antoniojpmarin/LoRa-NBIoT-Gateway/hardware/esquematicos_tfg.kicad_sch

## KiCad design hardware/esquematicos_tfg.kicad_sch (2026-03-21, last stored version)

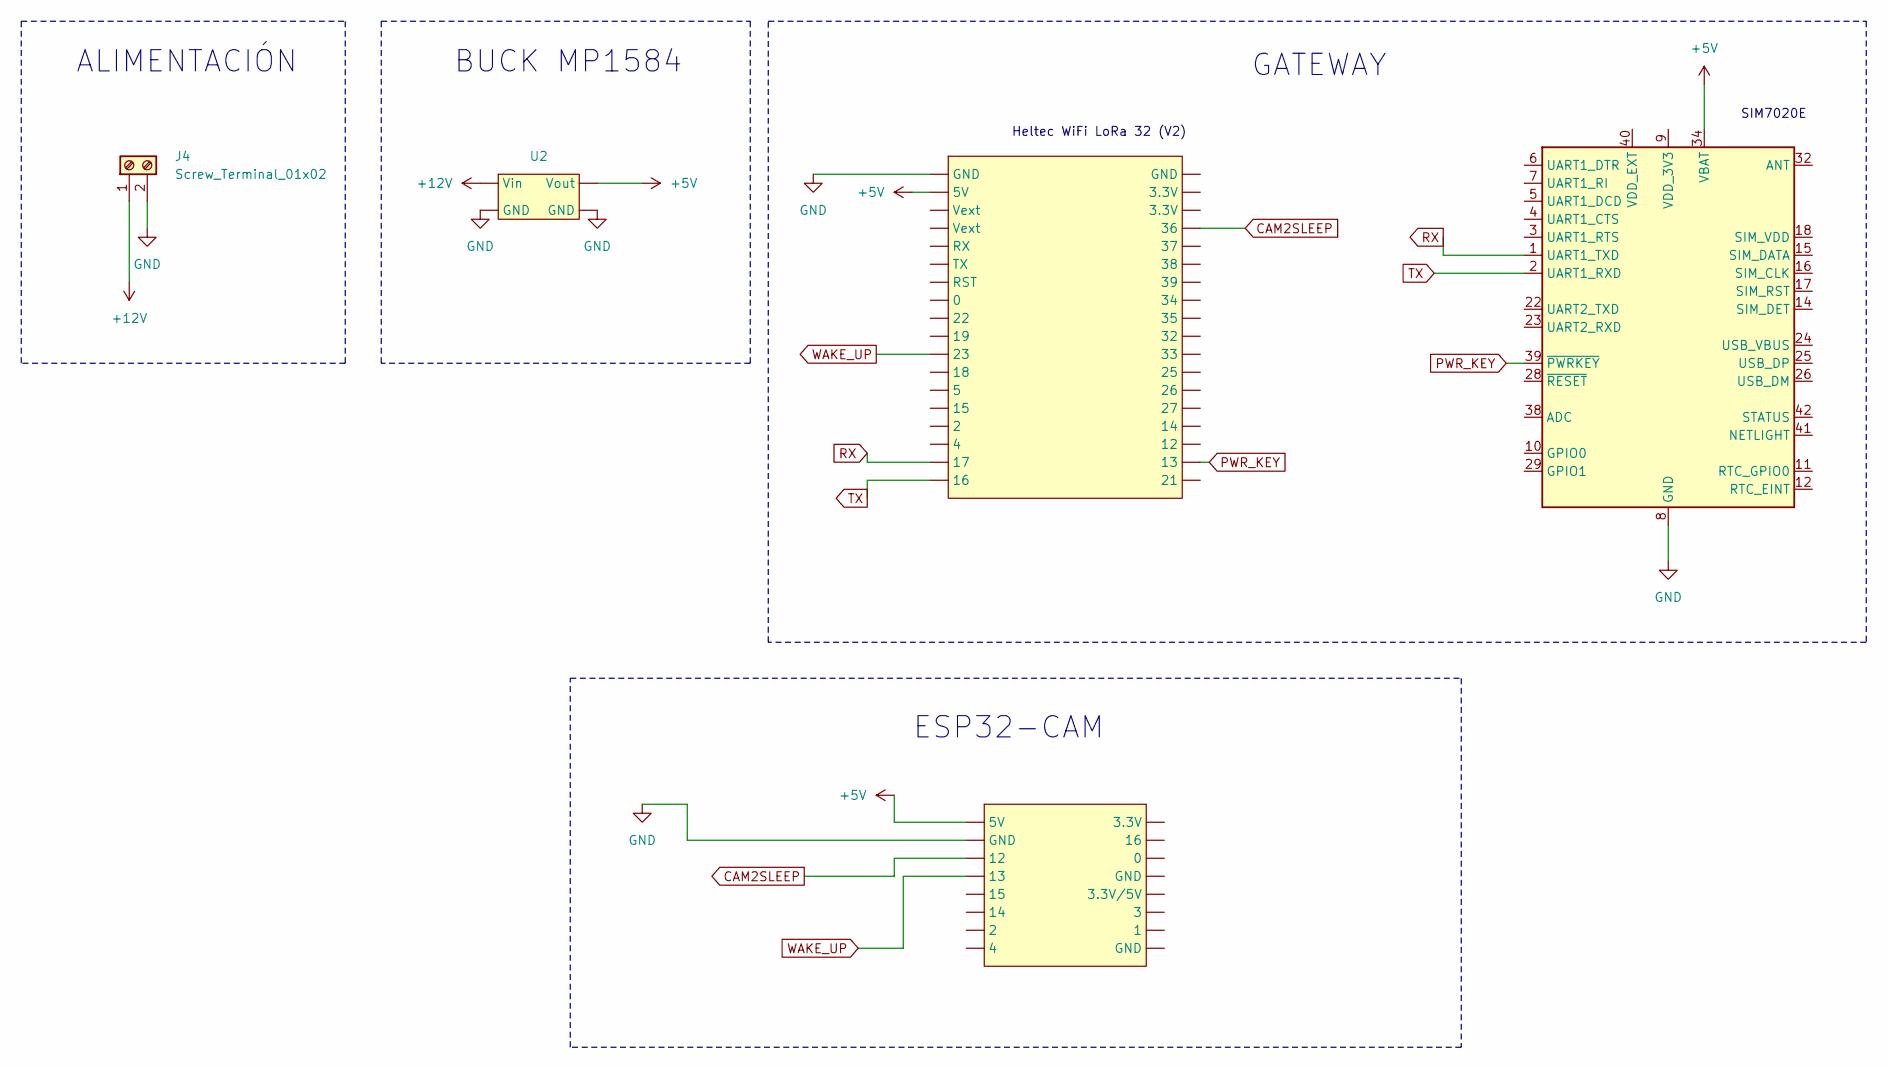
[picture p2: schematic esquematicos_tfg.kicad_sch]

Parts:
ESP32-CAM1: (no value)
Heltec_WiFi_LoRa_32_V1: (no value)
J4: Screw_Terminal_01x02
U1: SIM7020E; SIMCom_SIM800C
U2: (no value)

Connections:
+5V: ESP32-CAM1., Heltec_WiFi_LoRa_32_V1., U1.34 (VBAT), U1.35 (VBAT), U2.
+12V: J4.1, U2.
CAM2SLEEP: ESP32-CAM1., Heltec_WiFi_LoRa_32_V1.
GND: ESP32-CAM1., Heltec_WiFi_LoRa_32_V1., J4.2, U1.8 (GND), U1.13 (GND), U1.19 (GND), U1.21 (GND), U1.27 (GND), U1.30 (GND), U1.31 (GND), U1.33 (GND), U1.36 (GND), U1.37 (GND), U2.
PWR_KEY: Heltec_WiFi_LoRa_32_V1., U1.39 (~PWRKEY)
RX: Heltec_WiFi_LoRa_32_V1., U1.1 (UART1_TXD)
TX: Heltec_WiFi_LoRa_32_V1., U1.2 (UART1_RXD)
WAKE_UP: ESP32-CAM1., Heltec_WiFi_LoRa_32_V1.

Notes on the sheet:
ESP32-CAM
BUCK MP1584
SIM7020E
GATEWAY
ALIMENTACIÓN
Heltec WiFi LoRa 32 (V2)
